JaredMindlin/Interactive-Balance-Board-/Models and Schematics/Montessori_Schematic.kicad_sch

## KiCad design Models and Schematics/Montessori_Schematic.kicad_sch (2025-04-15)

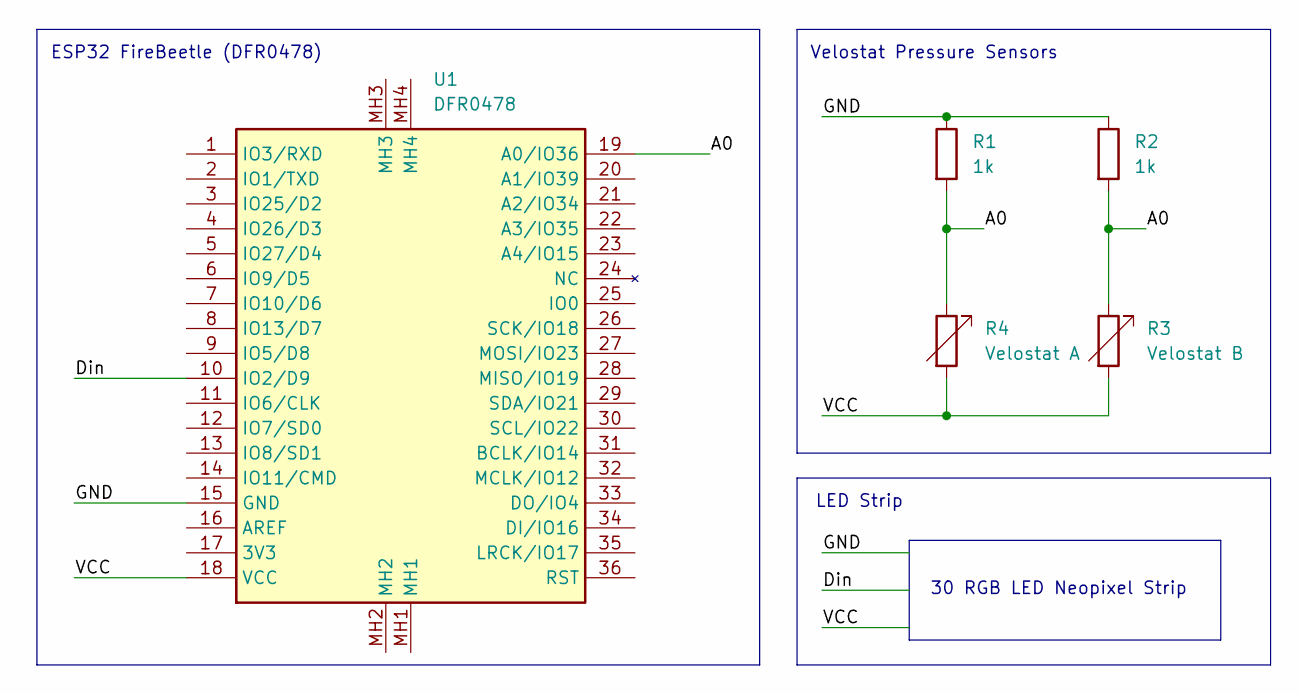
[picture p11: schematic Montessori_Schematic.kicad_sch]

Parts:
R1, R2: 1k
R3: Velostat B
R4: Velostat A
U1: DFR0478; FIREBEETLE_ESP32; Manufacturer_Part_Number DFR0478; Mouser Part Number 426-DFR0478

Connections:
A0: R1.2, R2.2, R3.1, R4.1, U1.19 (A0/IO36)
Din: U1.10 (IO2/D9)
GND: R1.1, R2.1, U1.15 (GND)
VCC: R3.2, R4.2, U1.18 (VCC)

Notes on the sheet:
30 RGB LED Neopixel Strip
Velostat Pressure Sensors
ESP32 FireBeetle (DFR0478)
LED Strip
